afiskon/hbr-mk2/images/bpfs/10.png

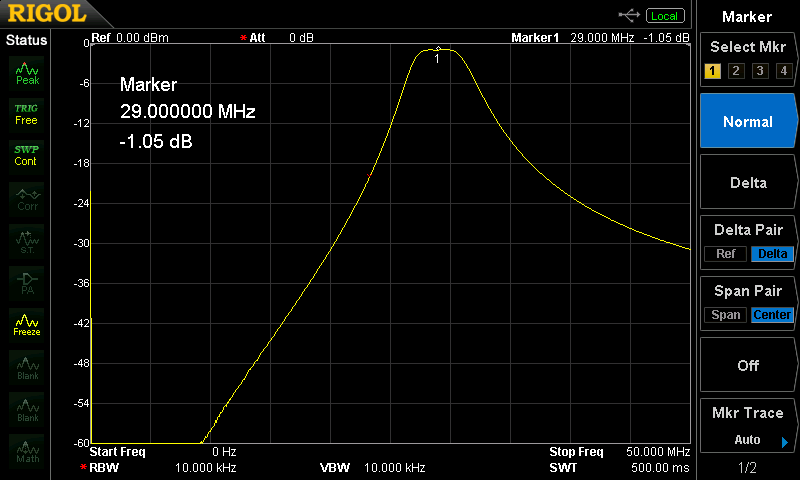
images/bpfs/10.png
