afiskon/hbr-mk2/images/bpfs/12.png

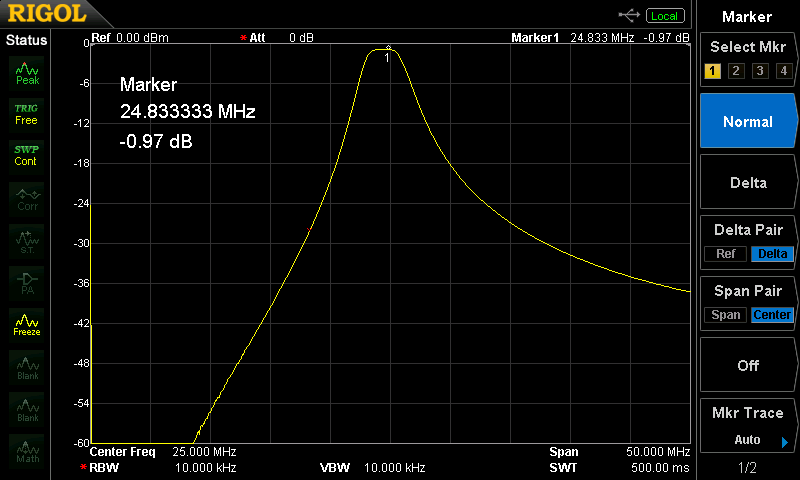
images/bpfs/12.png
