afiskon/hbr-mk2/images/bpfs/15.png

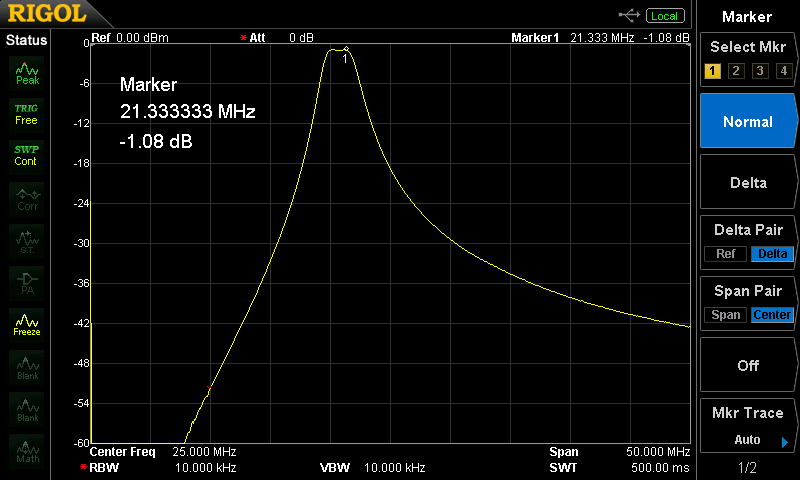
images/bpfs/15.png
