afiskon/hbr-mk2/images/bpfs/17.png

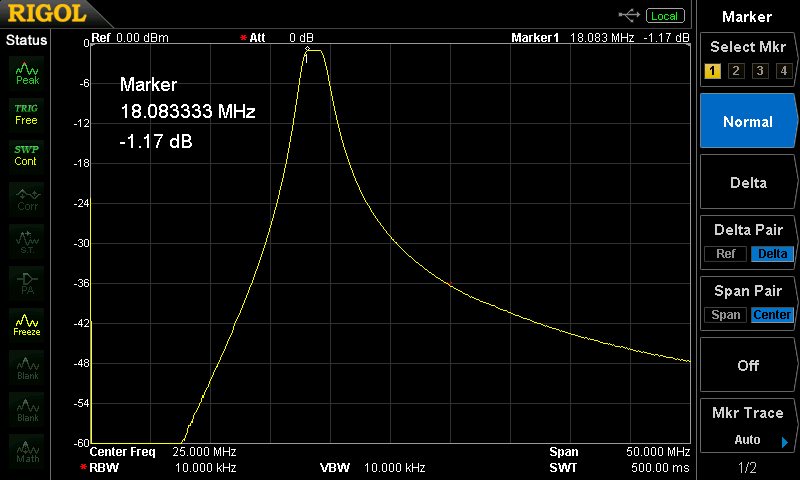
images/bpfs/17.png
