afiskon/hbr-mk2/images/bpfs/20.png

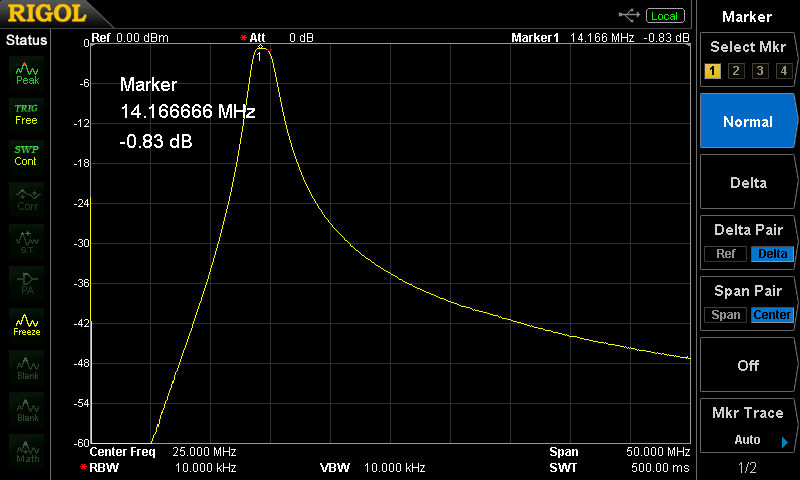
images/bpfs/20.png
