afiskon/hbr-mk2/images/bpfs/30.png

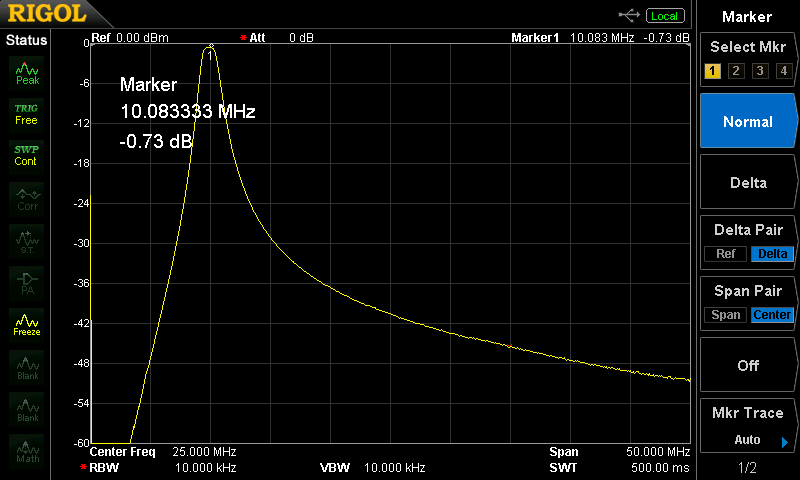
images/bpfs/30.png
