afiskon/hbr-mk2/images/bpfs/40.png

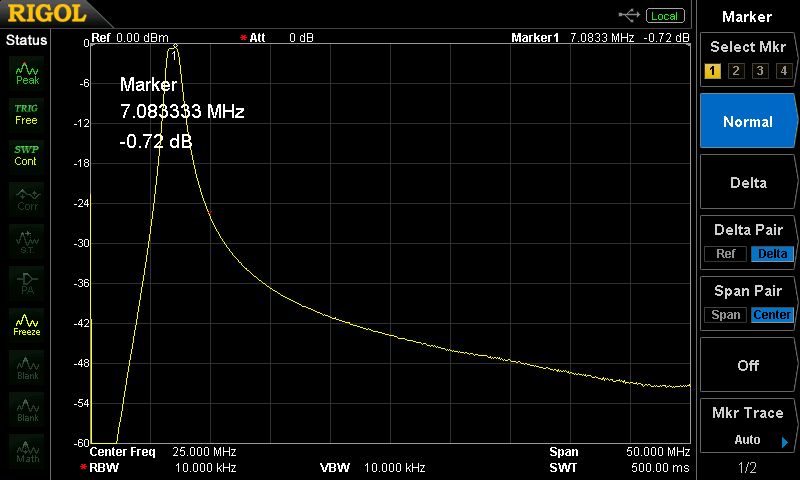
images/bpfs/40.png
