afiskon/hbr-mk2/images/bpfs/80.png

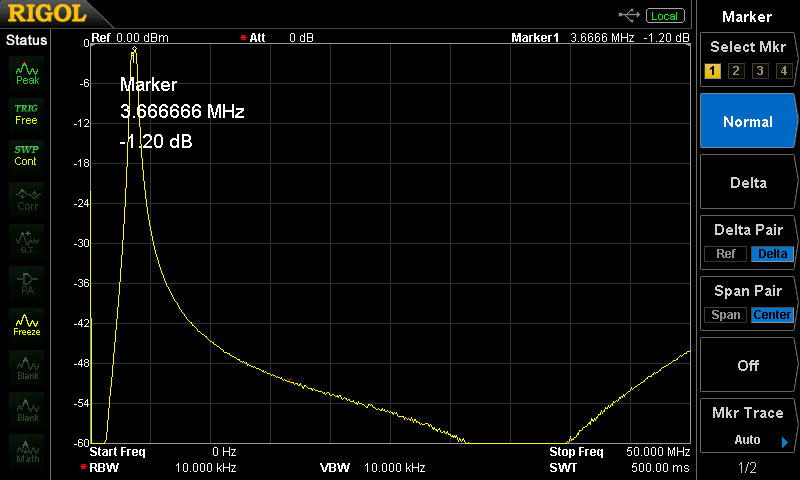
images/bpfs/80.png
