afiskon/hbr-mk2/images/enclosure/internals.jpg

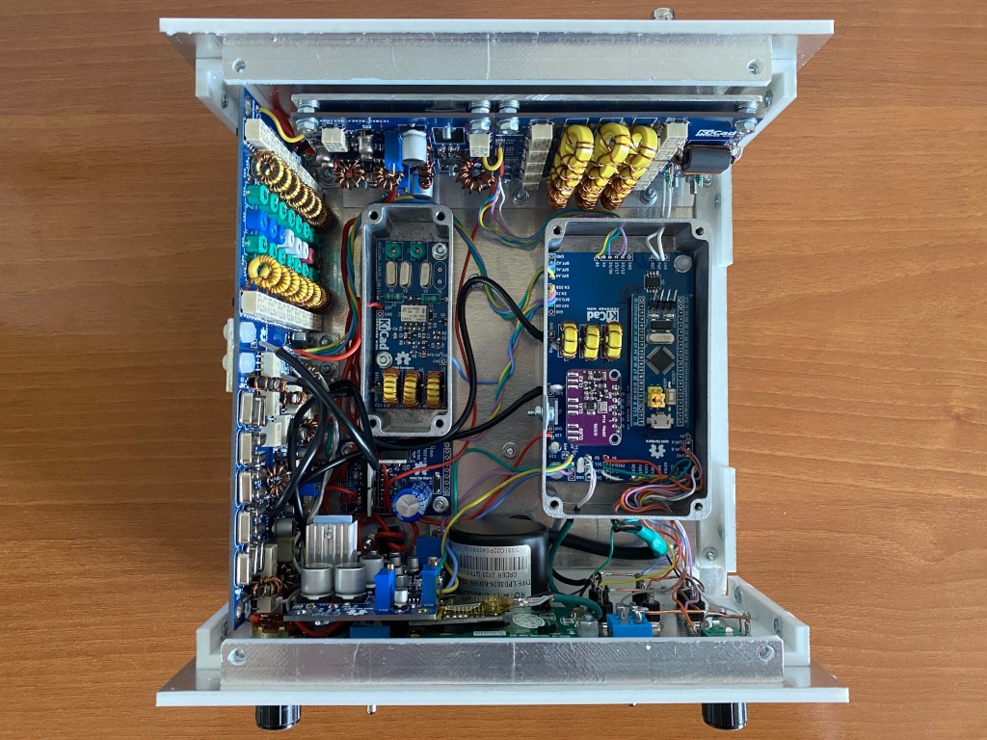
images/enclosure/internals.jpg
