afiskon/hbr-mk2/images/lpfs/40.png

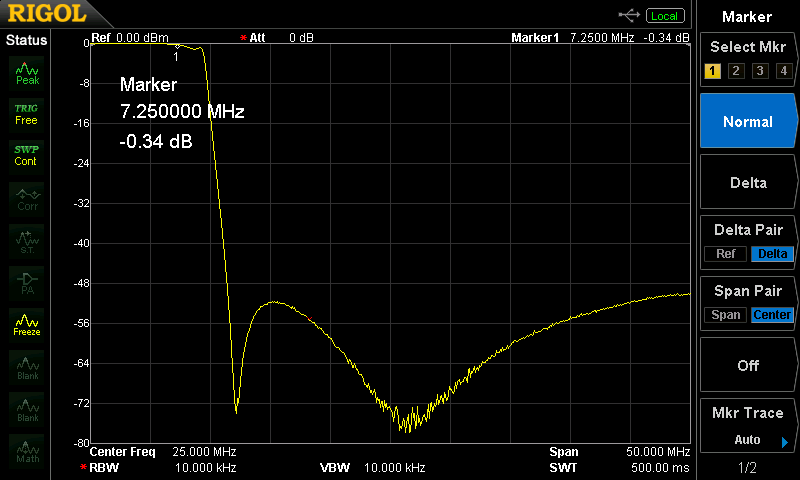
images/lpfs/40.png
