afiskon/hbr-mk2/images/lpfs/80.png

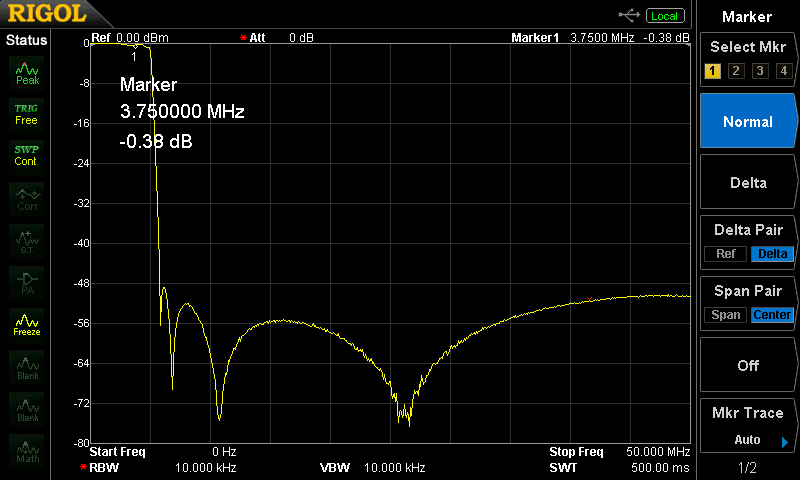
images/lpfs/80.png
