afiskon/hbr-mk2/images/lpfs/1210.png

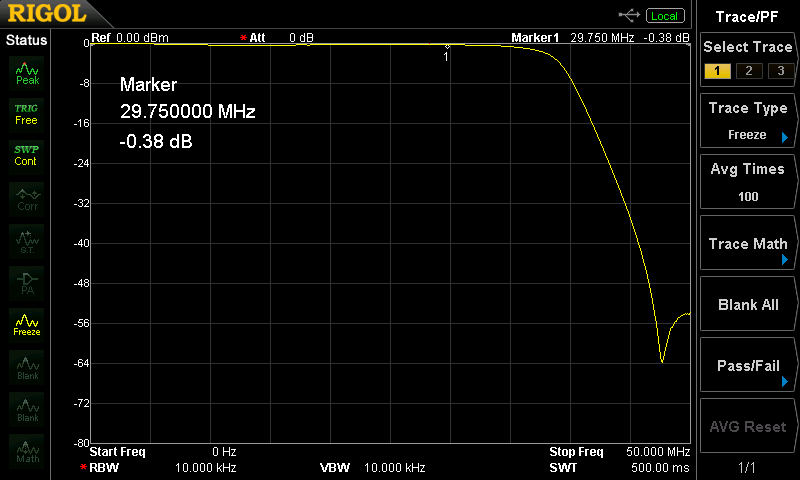
images/lpfs/1210.png
