afiskon/hbr-mk2/images/lpfs/1517.png

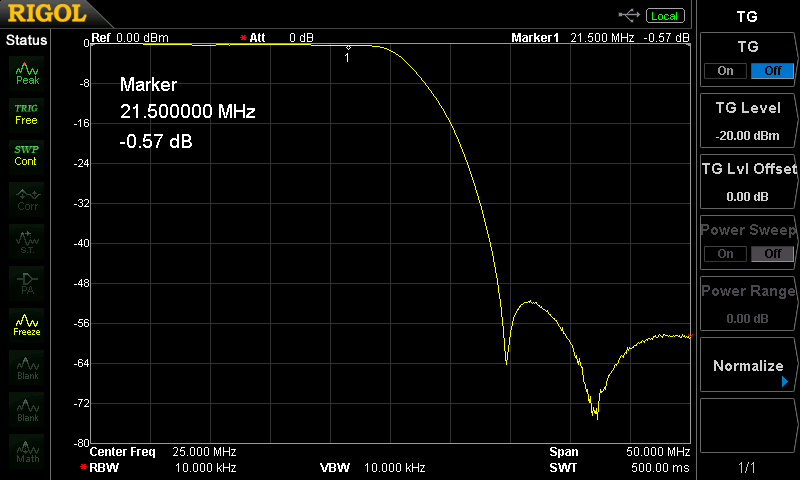
images/lpfs/1517.png
