afiskon/hbr-mk2/images/lpfs/2030.png

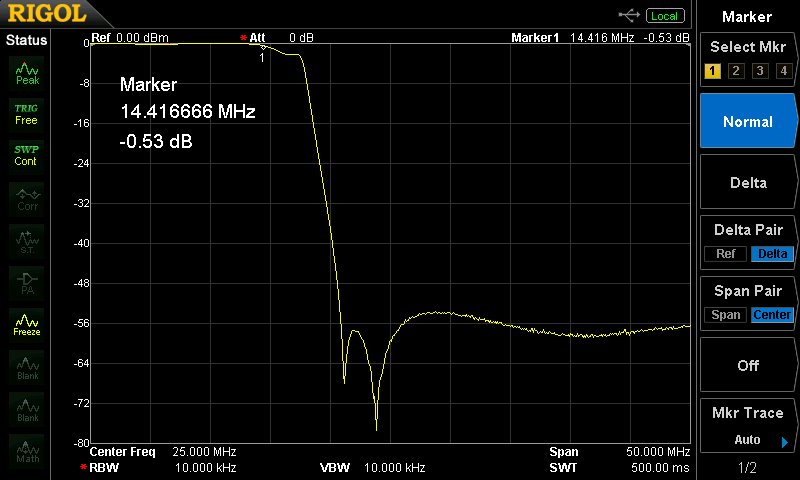
images/lpfs/2030.png
