afiskon/hbr-mk2/images/power/cw/10.png

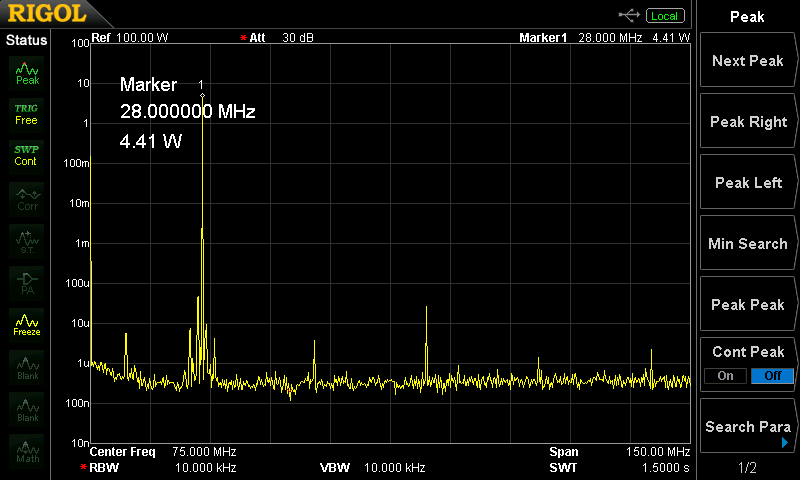
images/power/cw/10.png
