afiskon/hbr-mk2/images/power/cw/12.png

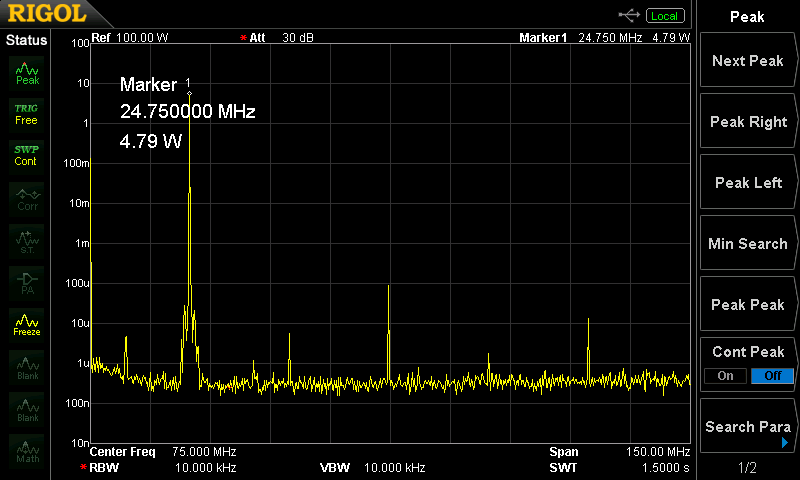
images/power/cw/12.png
