afiskon/hbr-mk2/images/power/cw/15.png

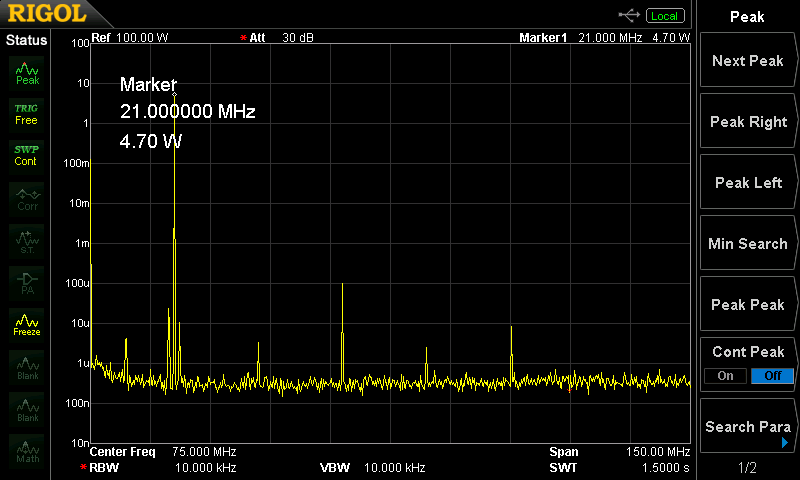
images/power/cw/15.png
