afiskon/hbr-mk2/images/power/cw/20.png

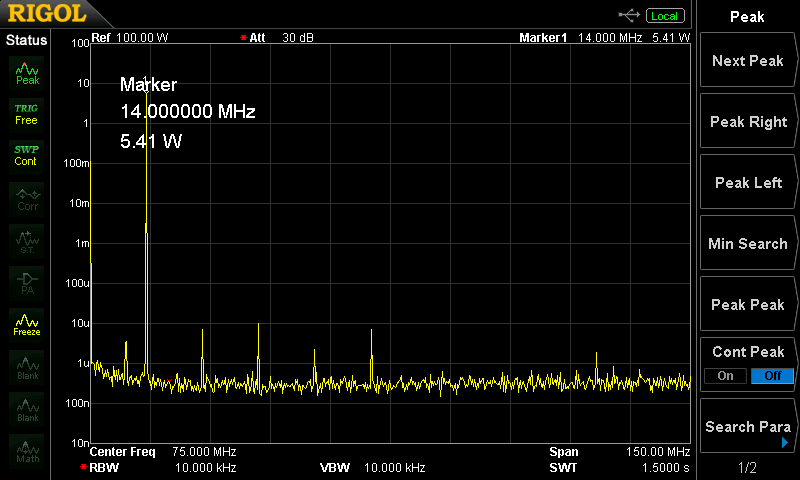
images/power/cw/20.png
