afiskon/hbr-mk2/images/power/cw/40.png

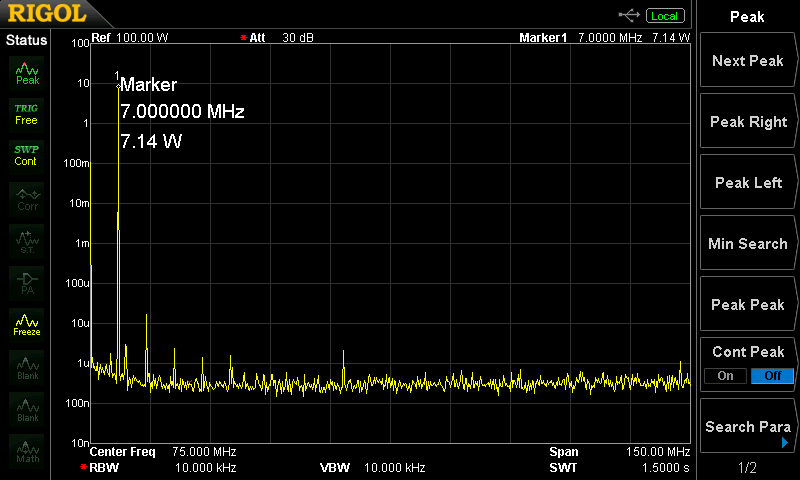
images/power/cw/40.png
