afiskon/hbr-mk2/images/power/ssb/10.png

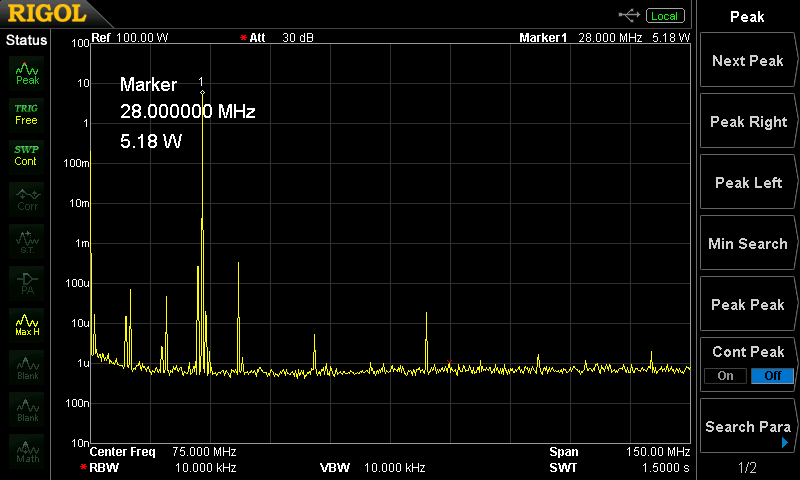
images/power/ssb/10.png
