afiskon/hbr-mk2/images/power/ssb/12.png

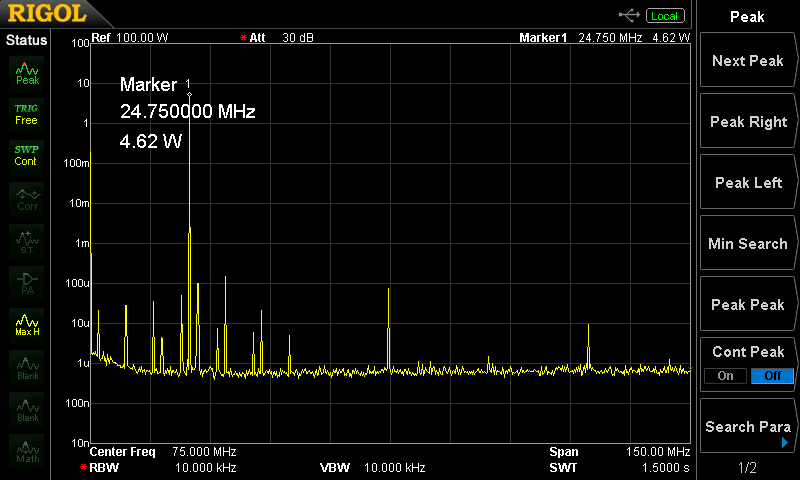
images/power/ssb/12.png
