afiskon/hbr-mk2/images/power/ssb/15.png

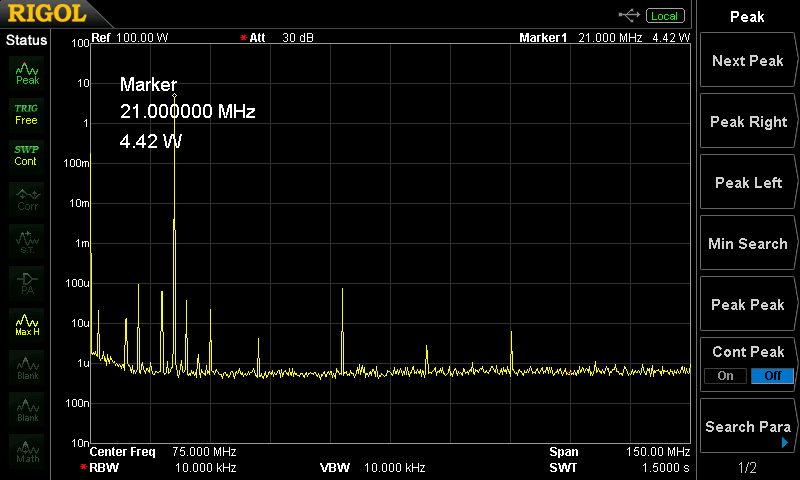
images/power/ssb/15.png
