afiskon/hbr-mk2/images/power/ssb/17.png

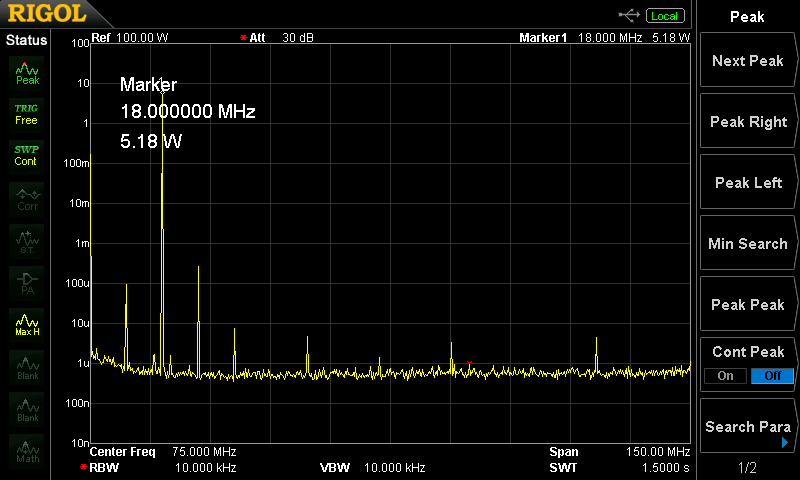
images/power/ssb/17.png
