afiskon/hbr-mk2/images/power/ssb/40.png

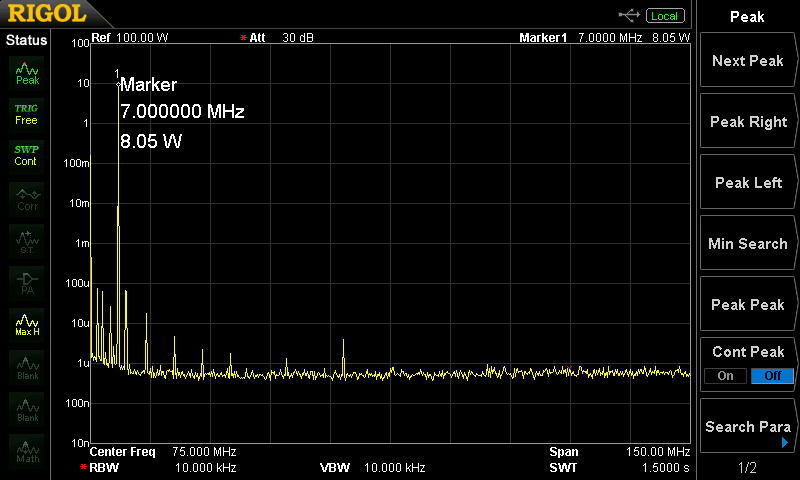
images/power/ssb/40.png
